Eljily-Mohamed/TempControlSystem/cablage/image_1.jpeg

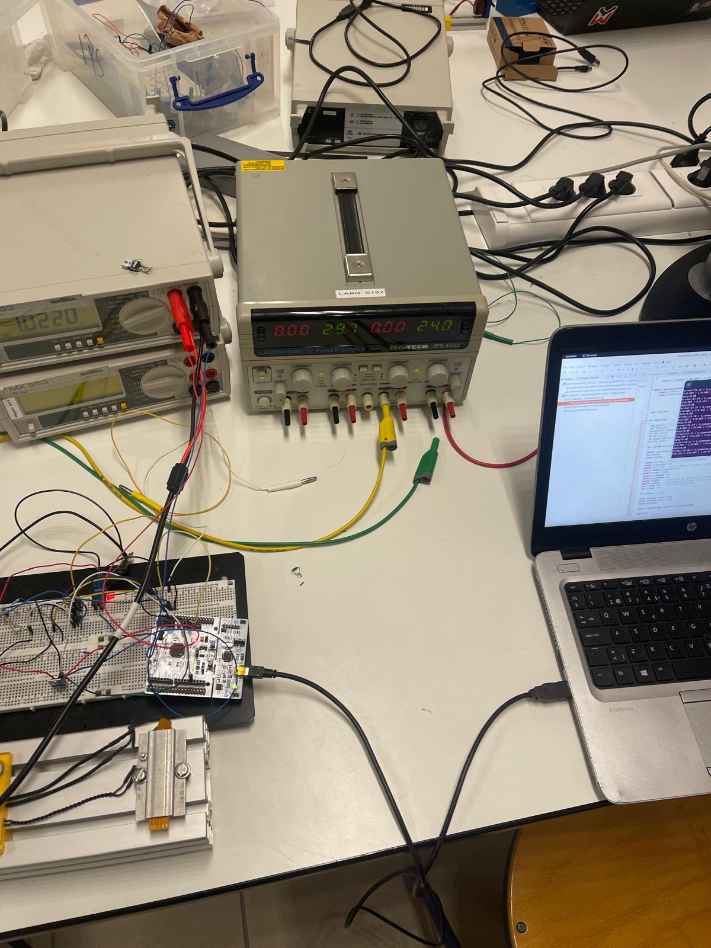
cablage/image_1.jpeg
