Eljily-Mohamed/TempControlSystem/cablage/image_2.jpeg

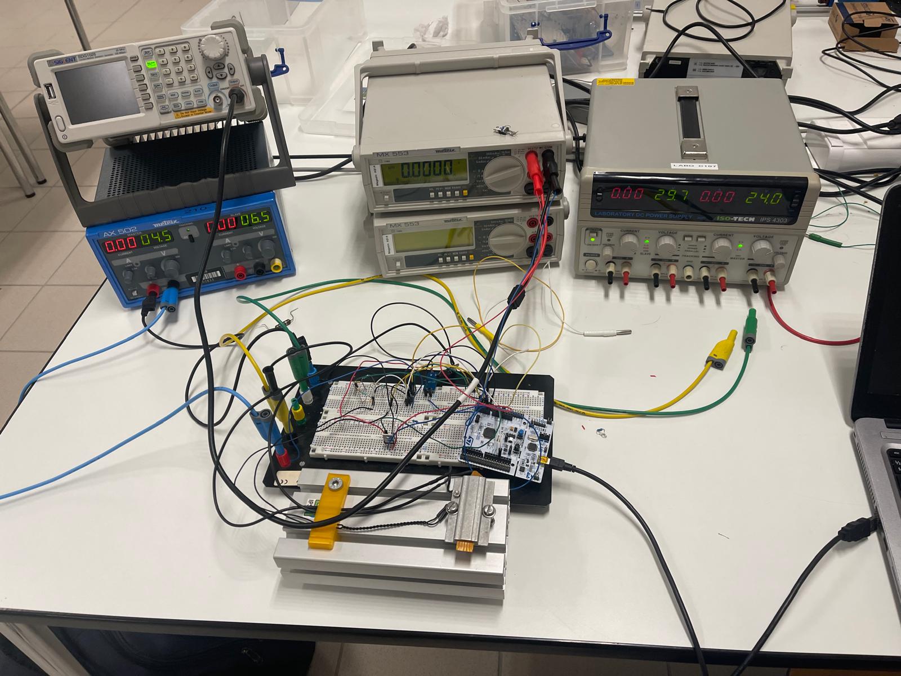
cablage/image_2.jpeg
