Eljily-Mohamed/TempControlSystem/cablage/image_3.jpeg

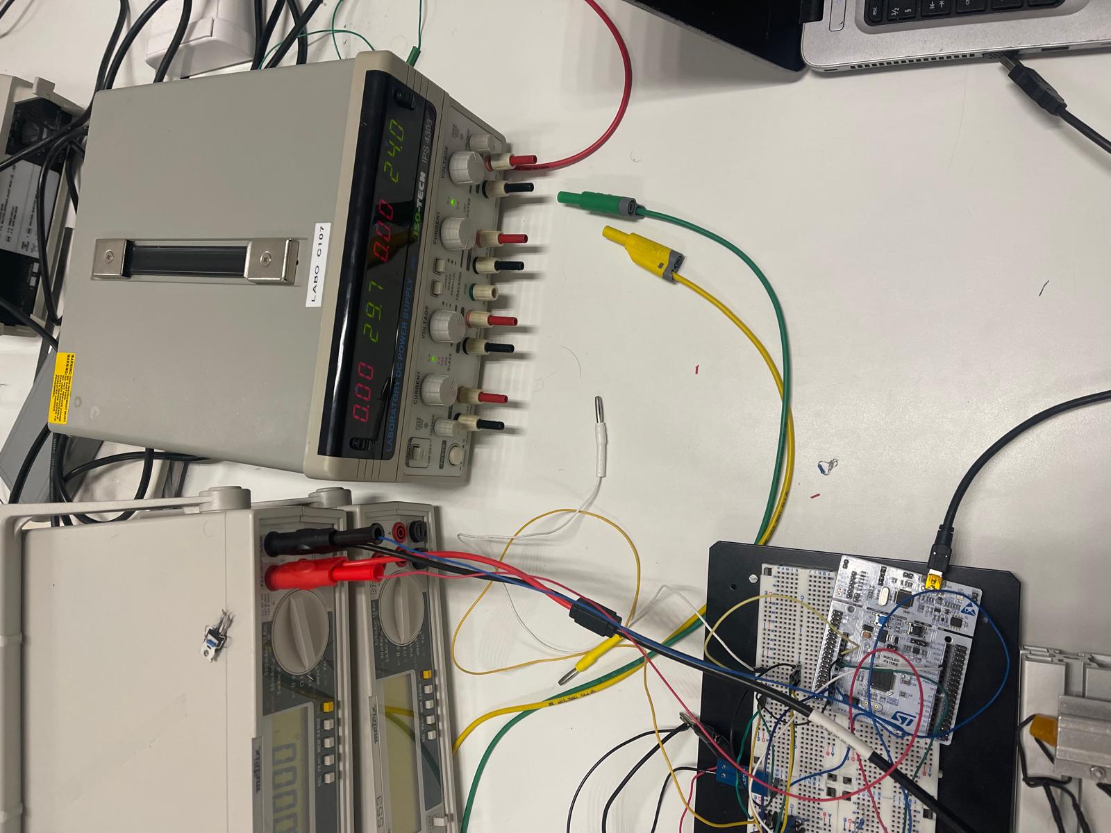
cablage/image_3.jpeg
