Eljily-Mohamed/TempControlSystem/cablage/image_4.jpeg

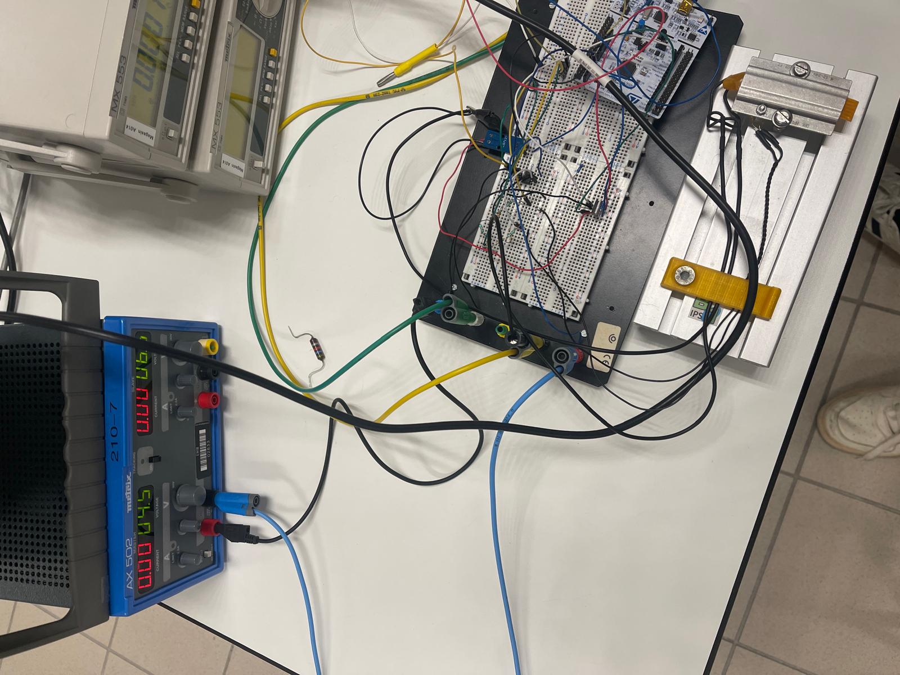
cablage/image_4.jpeg
