Eljily-Mohamed/TempControlSystem/cablage/image_5.jpeg

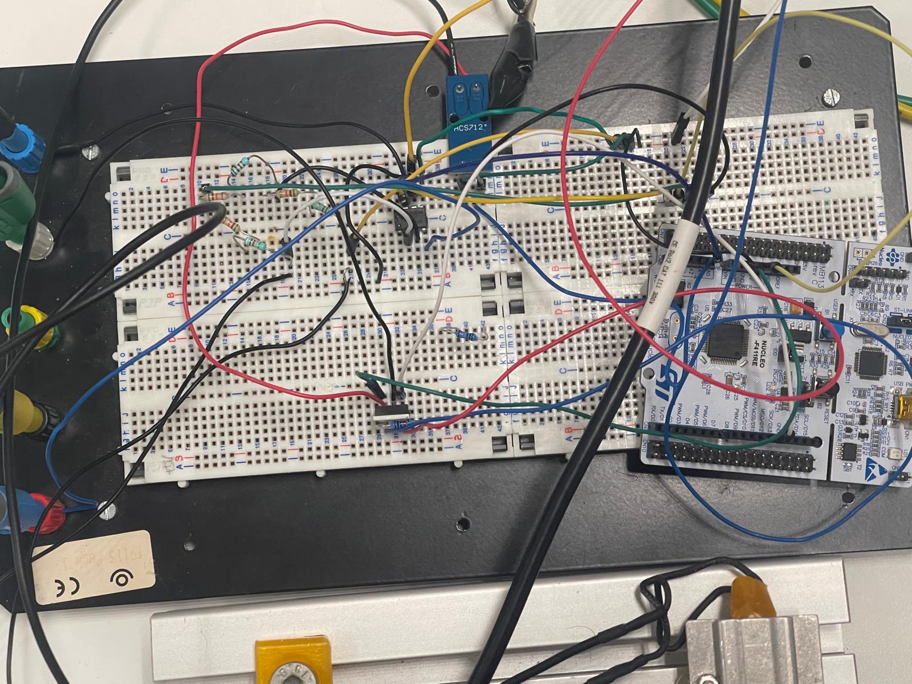
cablage/image_5.jpeg
