Eljily-Mohamed/TempControlSystem/cablage/image_6.jpeg

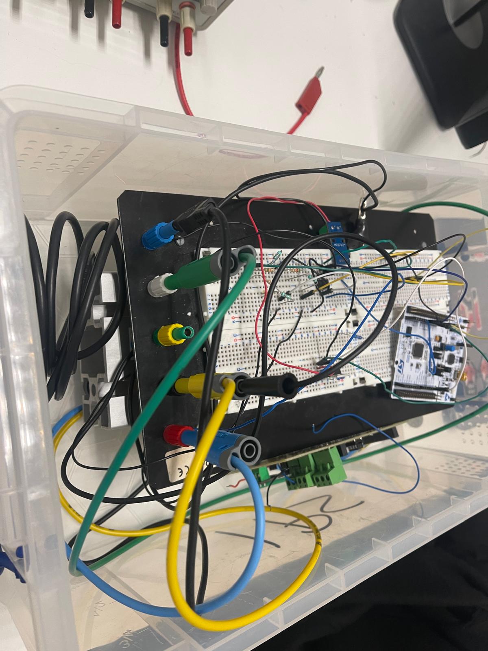
cablage/image_6.jpeg
