Eljily-Mohamed/TempControlSystem/cablage/pont_wheston.jpeg

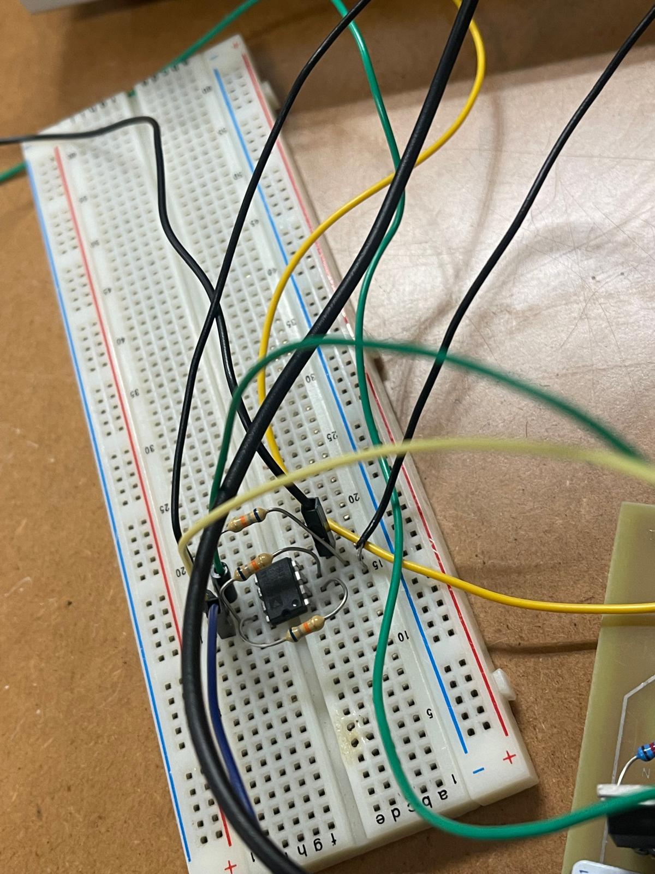
cablage/pont_wheston.jpeg
