Eljily-Mohamed/TempControlSystem/presentation/documentation/docs/images/thermistance.png

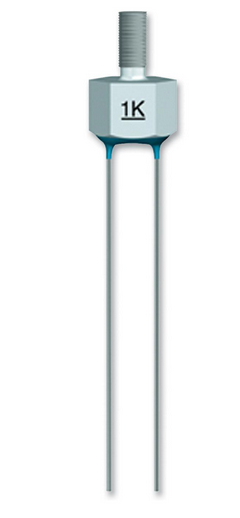
presentation/documentation/docs/images/thermistance.png
