Eljily-Mohamed/TempControlSystem/videos/demo_minicom.jpeg

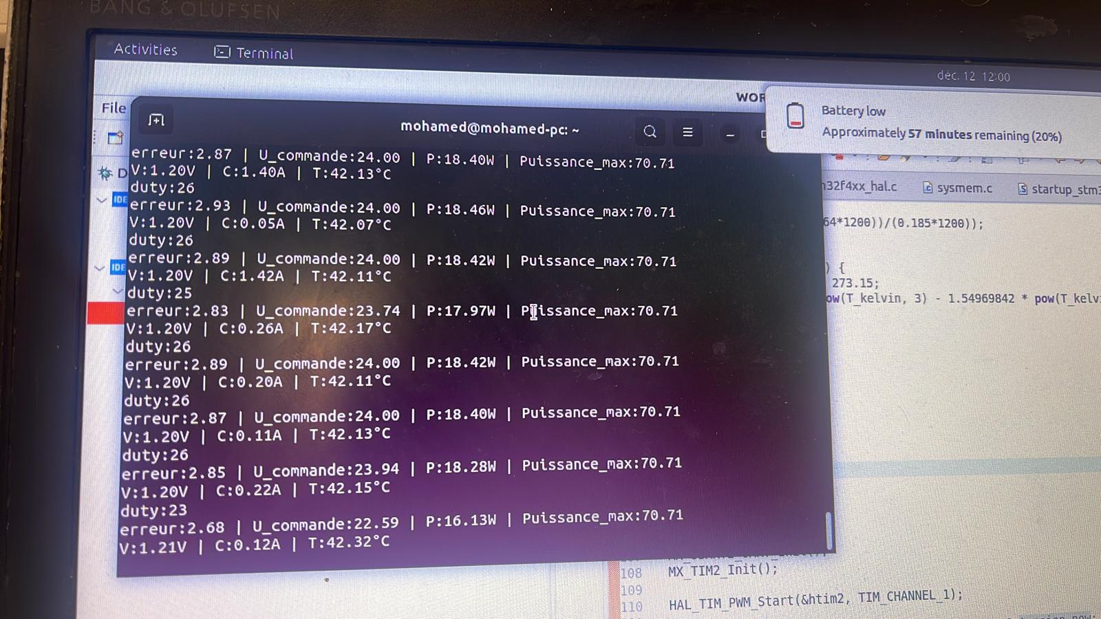
videos/demo_minicom.jpeg
